lucasfini/SmartHome/images/Breadboard1.png

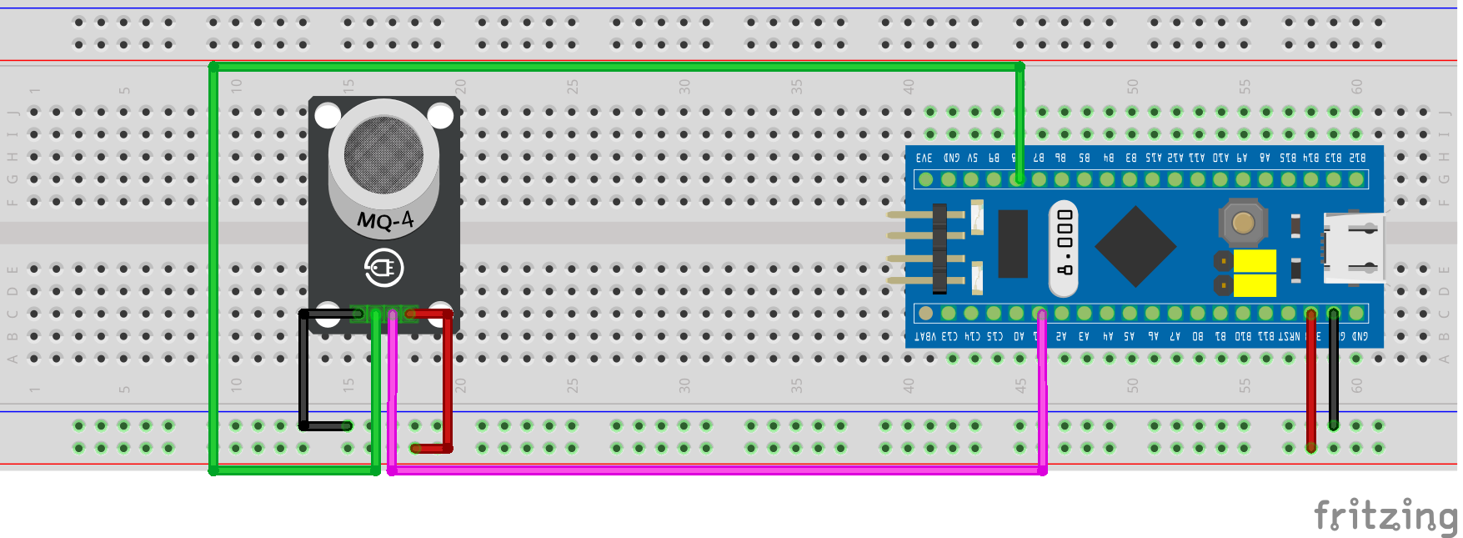
images/Breadboard1.png
