lucasfini/SmartHome/images/PCB3.png

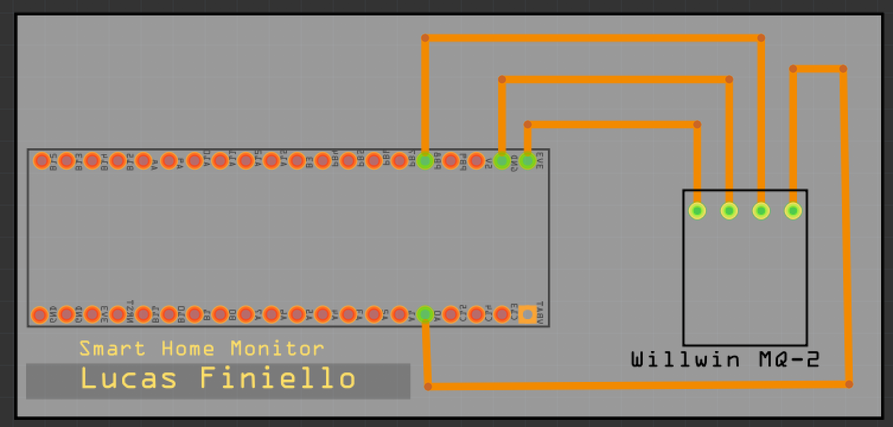
images/PCB3.png
