lucasfini/SmartHome/images/PCB.png

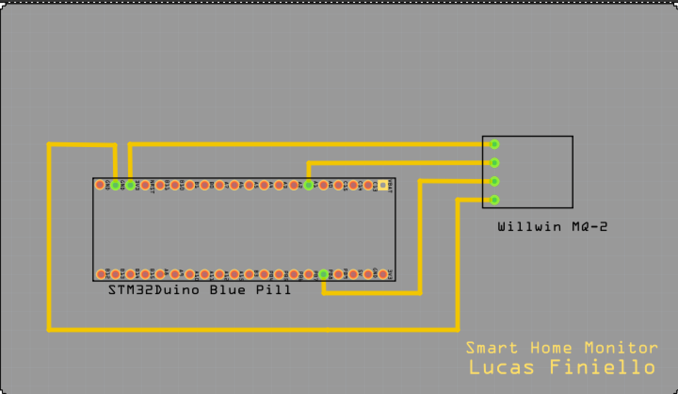
images/PCB.png
