lucasfini/SmartHome/images/tool.png

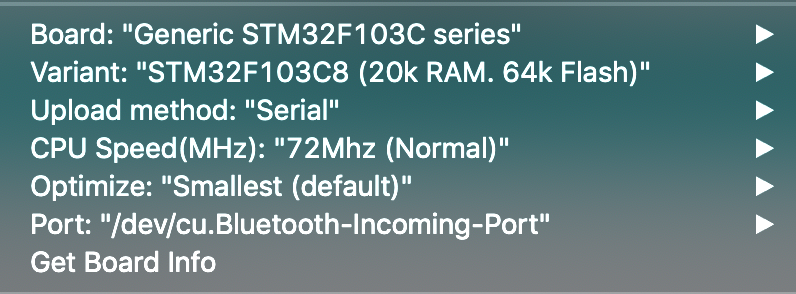
images/tool.png
